julian4596/bambu-playground/output/reference-match/lightest-2x2-relief-bottom-angle.png

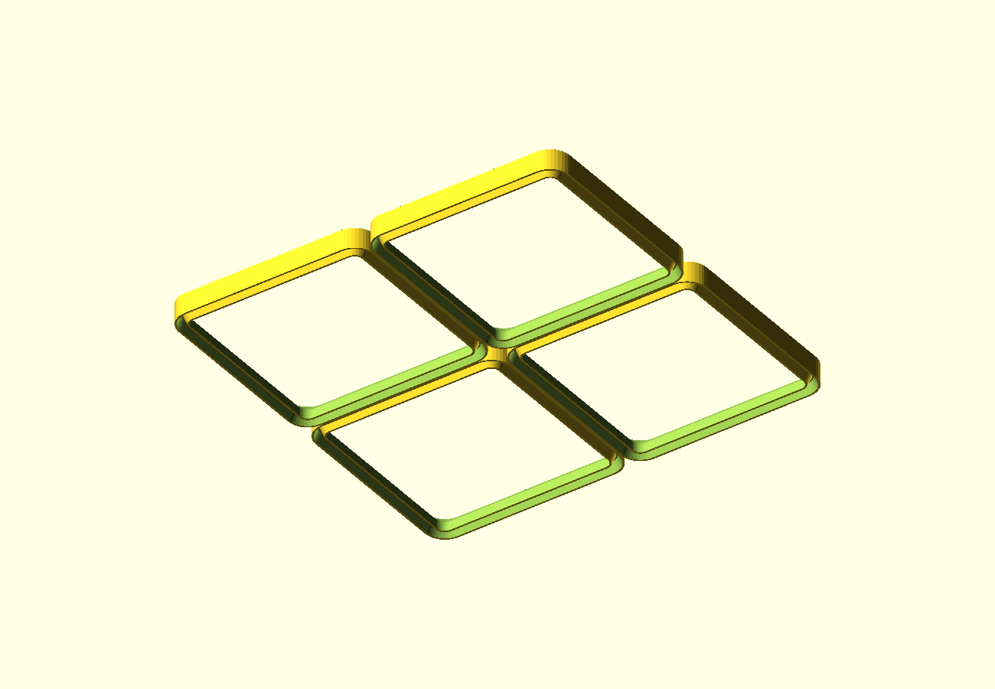
output/reference-match/lightest-2x2-relief-bottom-angle.png
